meyercm/polaris/src/compass.cpp

#include "compass.hpp"
#include <Wire.h>
namespace {
  const byte DEVICE_ADDRESS = 0x0E;
  const byte CTRL_REG_1 = 0x10;
  // register 1 options
  const byte ACTIVE=0x01;
  const byte TRIGGER=0x02;
  const byte FAST_READ=0x04;
  const byte OVER_SAMPLE_16 = 0x00;
  const byte OVER_SAMPLE_32 = 0x08;
  const byte OVER_SAMPLE_64 = 0x10;
  const byte OVER_SAMPLE_128 = 0x18;

  const byte CTRL_REG_2 = 0x11;
  // register 2 options
  const byte AUTO_RESET = 0x80;
  const byte RAW = 0x20;
  const byte MANUAL_RESET = 0x10;
}

void Compass::initialize(){
  Wire.begin();
  Wire.beginTransmission(DEVICE_ADDRESS);
  Wire.write(CTRL_REG_2);
  Wire.write(AUTO_RESET + RAW);
  Wire.endTransmission();
}

void Compass::request_measurement(){
  Wire.beginTransmission(DEVICE_ADDRESS);
  Wire.write(CTRL_REG_1);
  Wire.write(OVER_SAMPLE_128 + TRIGGER);
  Wire.endTransmission();
}

void Compass::read(){
  while(Wire.available() > 0){
    Wire.read(); // clear pending reads
  }
  Wire.beginTransmission(DEVICE_ADDRESS);
  Wire.write(byte(0x00));
  Wire.endTransmission(false);
  Wire.requestFrom(DEVICE_ADDRESS, 7);
  Wire.read(); // ready byte, must read, but can discard
  byte x1 = Wire.read();
  byte x2 = Wire.read();
  x = (x1 << 8) | x2;
  byte y1 = Wire.read();
  byte y2 = Wire.read();
  y = (y1 << 8) | y2;
  byte z1 = Wire.read();
  byte z2 = Wire.read();
  z = (z1 << 8) | z2;
  update_min_max(x, y, z);
}

void Compass::update_min_max(int x, int y, int z){
  // HACK: disable until we get t-digests
  return;
  if (x < min_x) {min_x = x;}
  if (y < min_y) {min_y = y;}
  if (z < min_z) {min_z = z;}
  if (x > max_x) {max_x = x;}
  if (y > max_y) {max_y = y;}
  if (z > max_z) {max_z = z;}
}

int Compass::get_x(){
  return ((x - min_x) / ((max_x - min_x) * 1.0)) * 510 - 255;
}
int Compass::get_y(){
  return ((y - min_y) / ((max_y - min_y) * 1.0)) * 510 - 255;
}
int Compass::get_z(){
  return ((z - min_z) / ((max_z - min_z) * 1.0)) * 510 - 255;
}
